danjperron/nRF24L01_With_Sensor/nRF24L01_DHT22.png

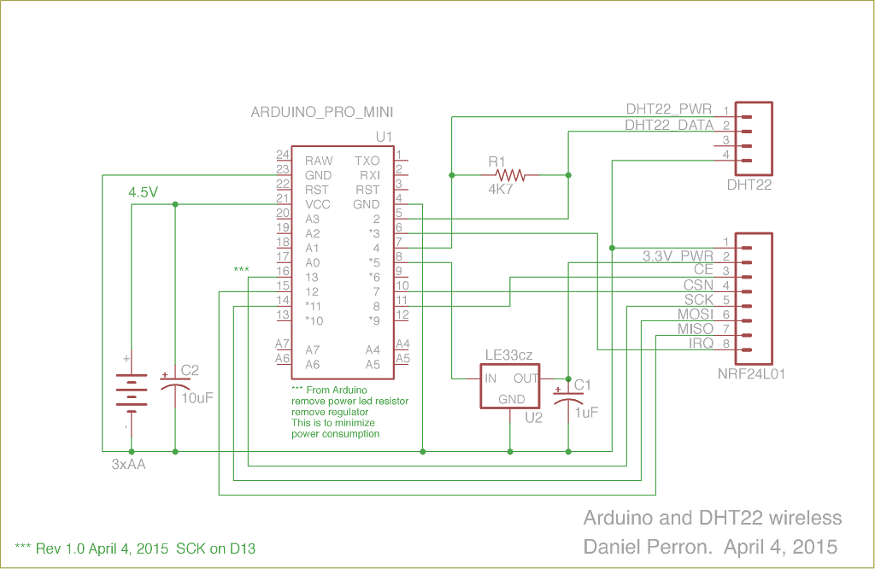
nRF24L01_DHT22.png
